ajohnson-97/Pi-Router/CAD Files/PNGs/admincontrol.png

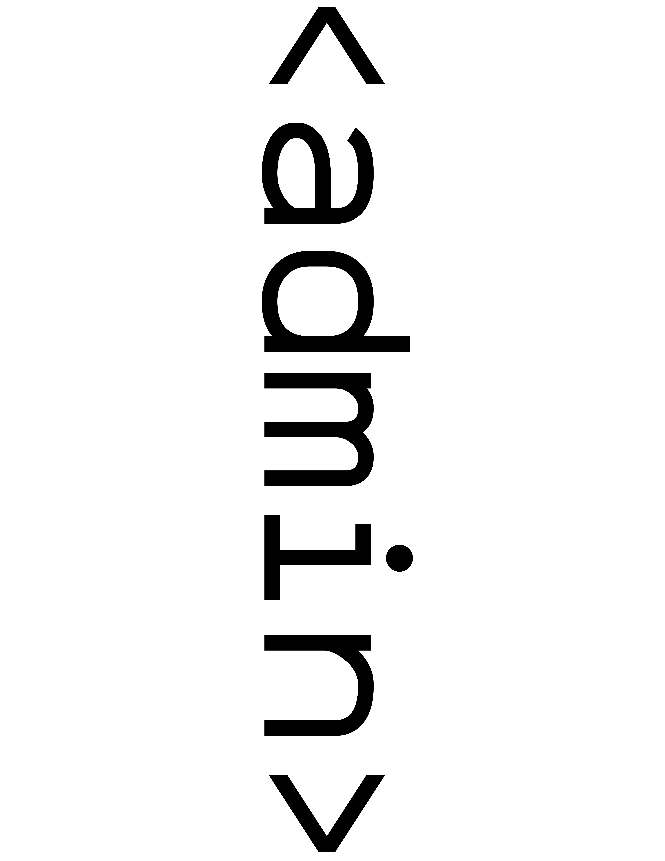
CAD Files/PNGs/admincontrol.png
