ajohnson-97/Pi-Router/CAD Files/PNGs/dns.png

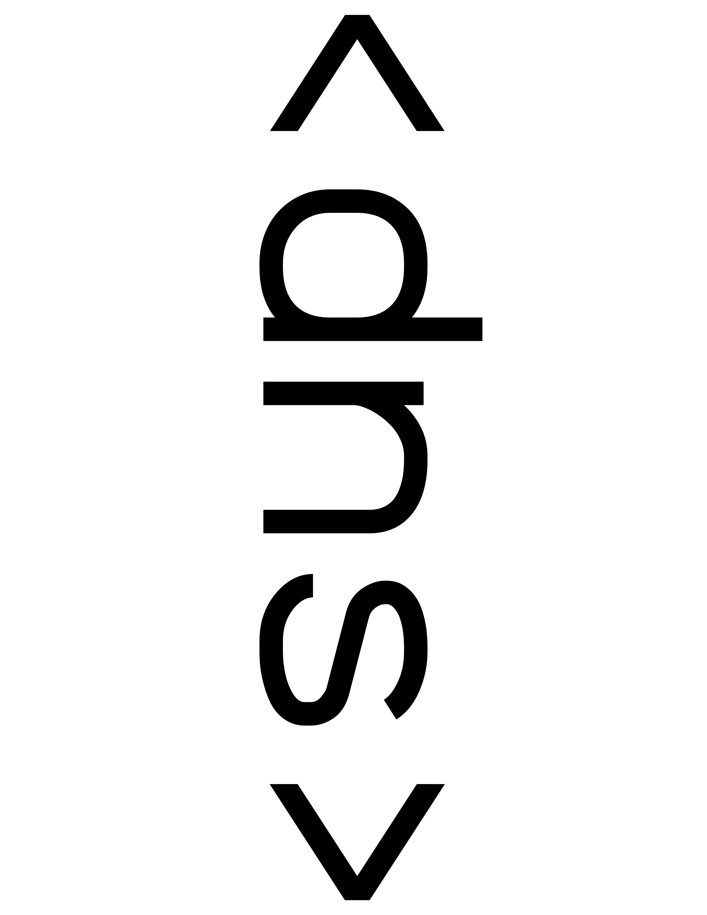
CAD Files/PNGs/dns.png
