ajohnson-97/Pi-Router/CAD Files/PNGs/fanborder.png.png

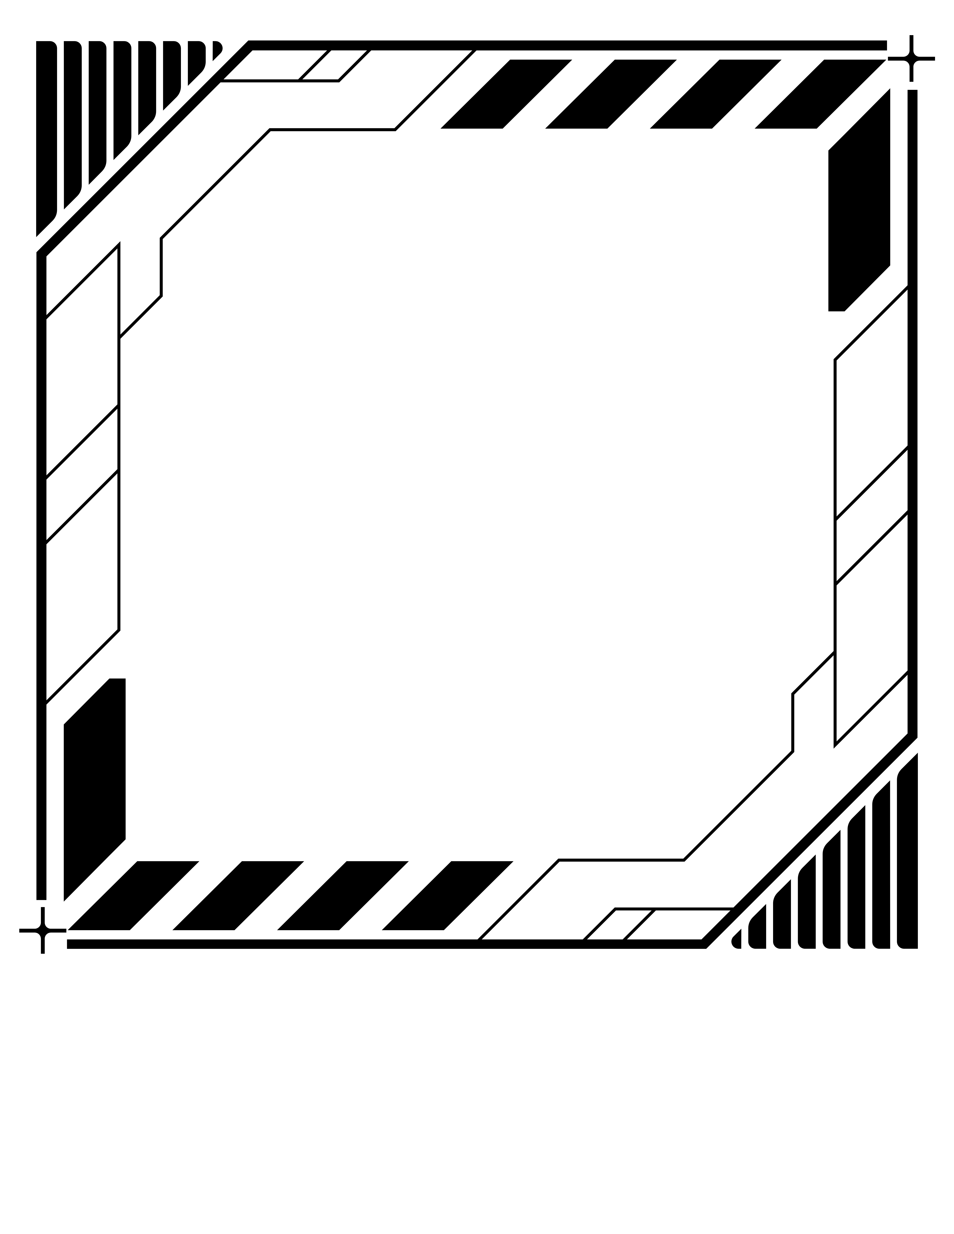
CAD Files/PNGs/fanborder.png.png
