ajohnson-97/Pi-Router/CAD Files/PNGs/technicaldetails.png

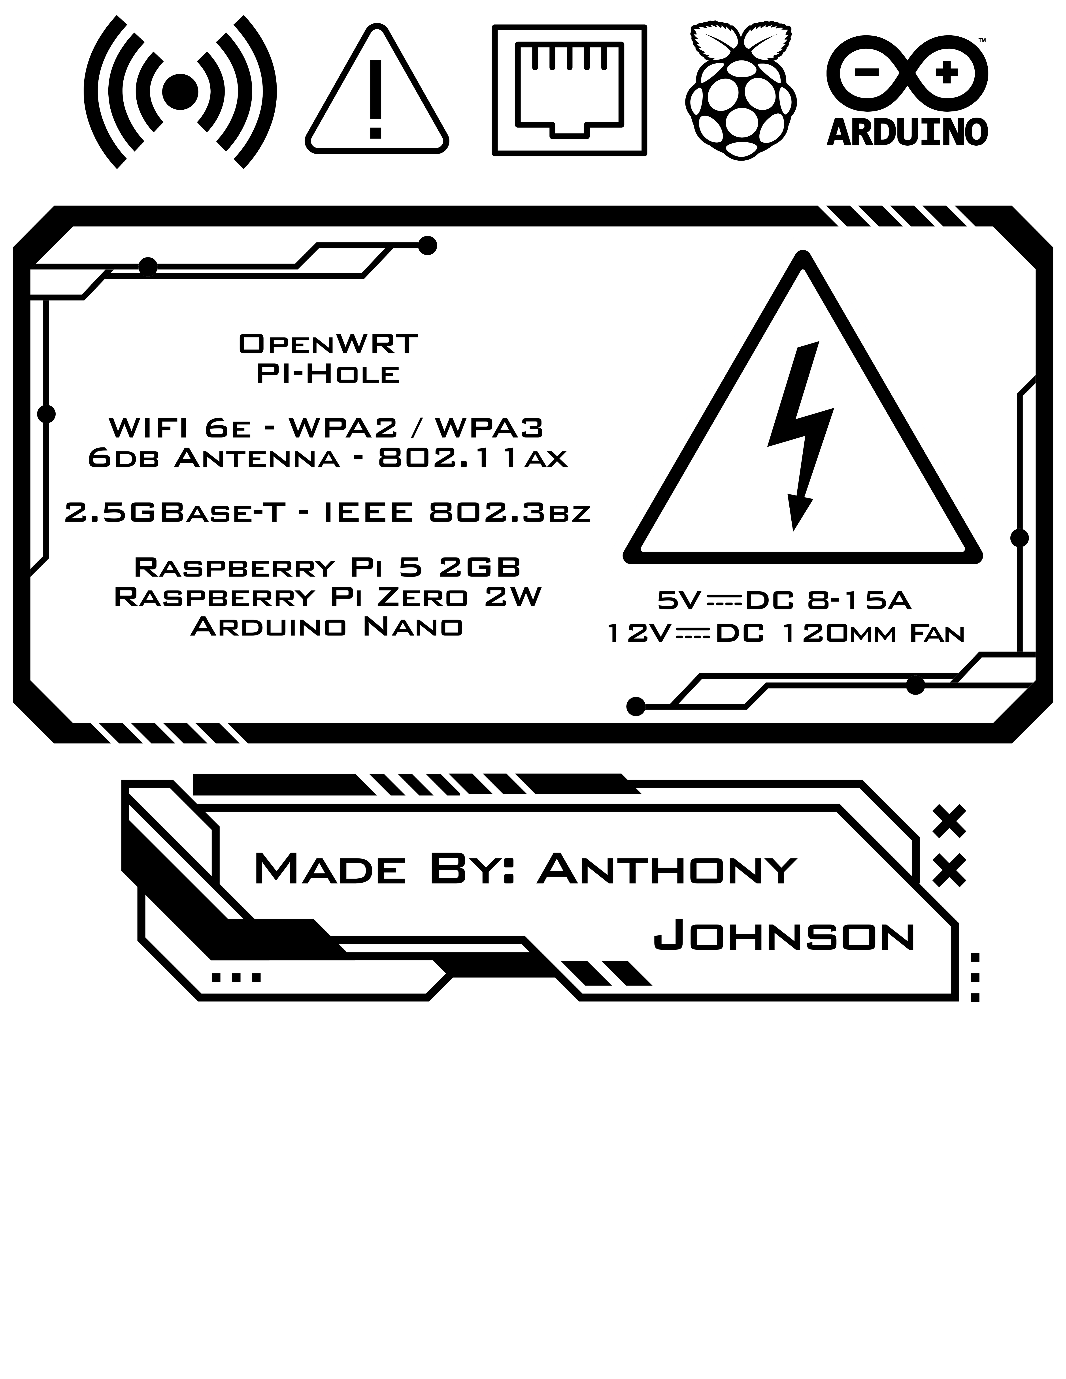
CAD Files/PNGs/technicaldetails.png
