ajohnson-97/Pi-Router/Electronics/Parts/Parts_List.png

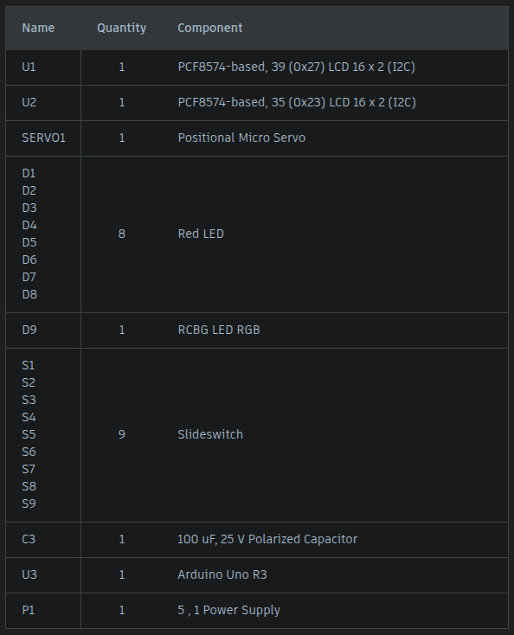
Electronics/Parts/Parts_List.png
