ajohnson-97/Pi-Router/Electronics/Schematics/Wiring_Diagram_TinkerCAD.png

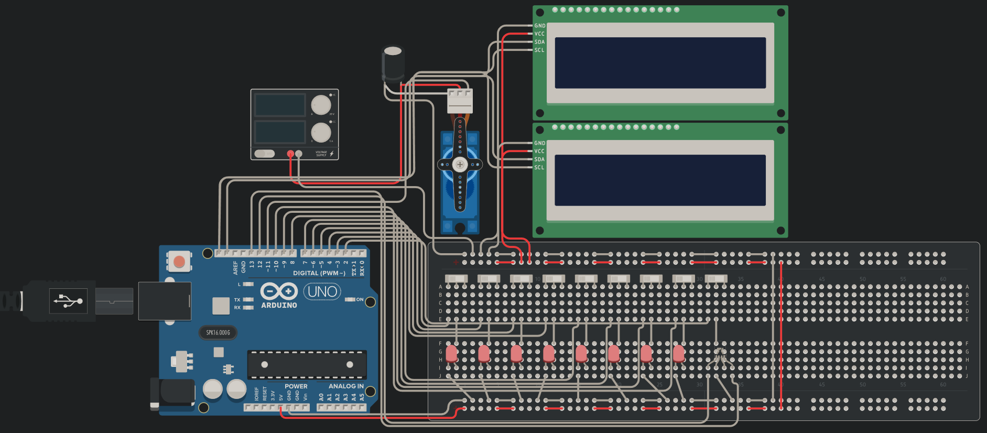
Electronics/Schematics/Wiring_Diagram_TinkerCAD.png
